datamann/GA-weather-station/Nextion Project files/images/radiosmall.png

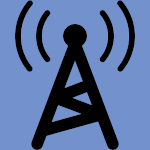
Nextion Project files/images/radiosmall.png
