datamann/GA-weather-station/Remote Sensor Power Waveform/pic_60_1.bmp

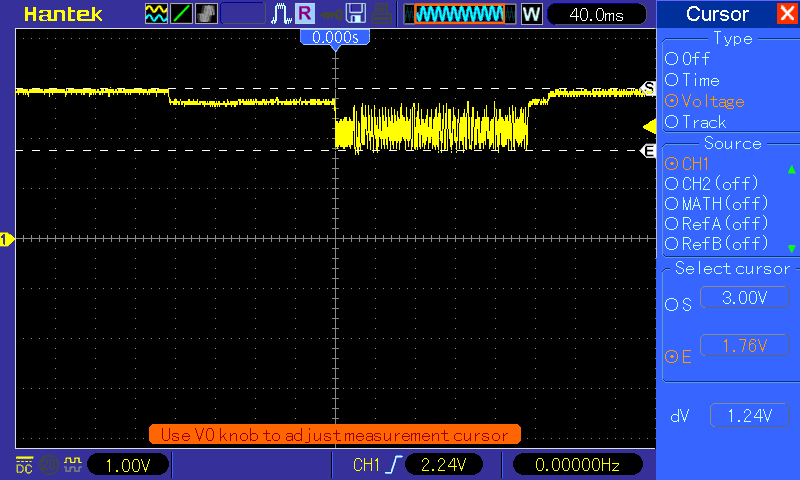
Remote Sensor Power Waveform/pic_60_1.bmp
