datamann/GA-weather-station/Remote Sensor Power Waveform/pic_60_3.bmp

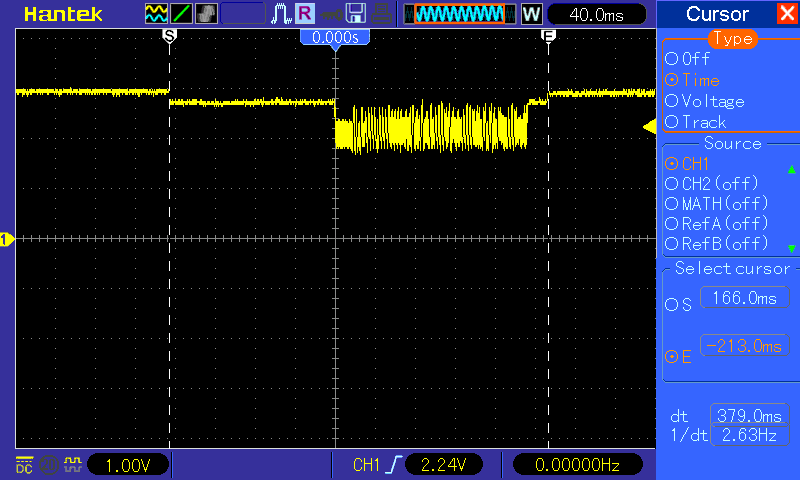
Remote Sensor Power Waveform/pic_60_3.bmp
