datamann/GA-weather-station/Remote Sensor Power Waveform/pic_60_4.bmp

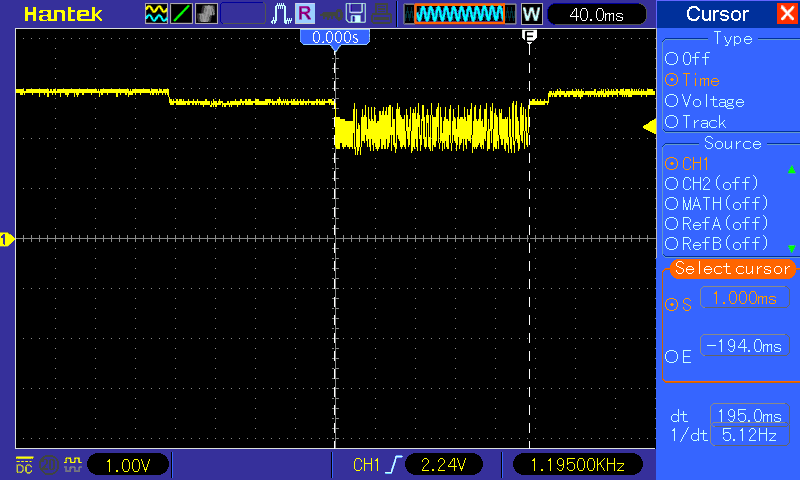
Remote Sensor Power Waveform/pic_60_4.bmp
