datamann/GA-weather-station/pictures/SIM7100E-breakout-board-EVB-board-development-Board-testing-board-B1-B3-B7-B8-B20-4G-LDD.jpg_Q90.jpg_.png

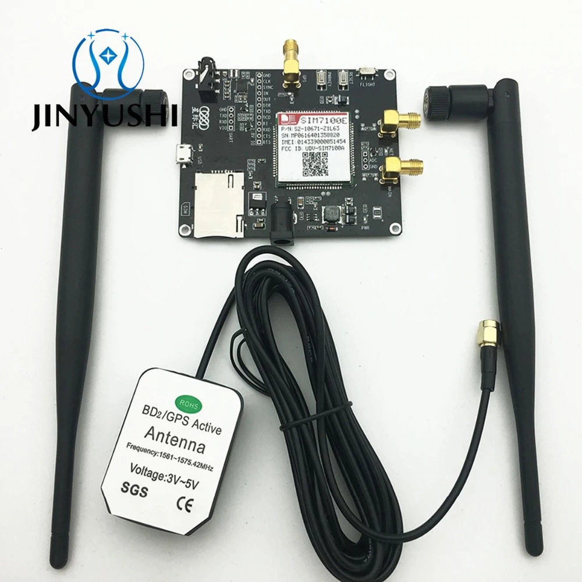
pictures/SIM7100E-breakout-board-EVB-board-development-Board-testing-board-B1-B3-B7-B8-B20-4G-LDD.jpg_Q90.jpg_.png
